wemaxon/es8390-breakout/sim/guitar_input_stage.asc

C1: cap; 100n
C2: cap; 100p
C3: cap; 1µ
C4: cap; 10p
R1: res; 1Meg
R2: res; 1Meg
R3: res; 4700
R4: res; 10k
R5: res; 10k
R6: res; 100k
R7: res; 100k
R8: res; 16k
U1: LTC6087
U2: LTC6087
V1: voltage; 3.3
V2: voltage; SINE(0 100m 440)
Named nets: 0, VCC, OUT, VBIAS
.tran 0.1
